morridm-zz/drumlights/images/20171210_095043.jpg

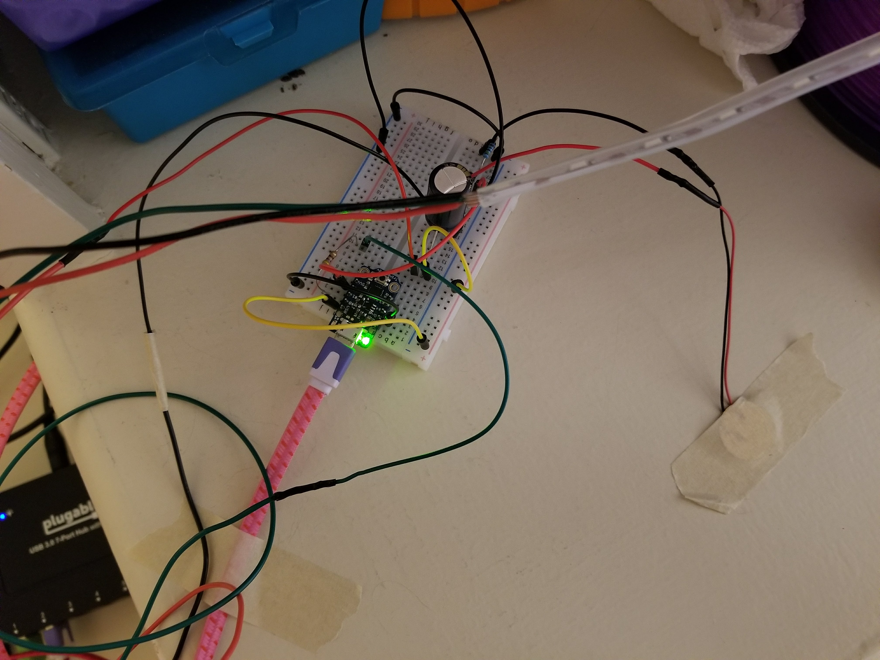
images/20171210_095043.jpg
