morridm-zz/drumlights/images/20171210_095117.jpg

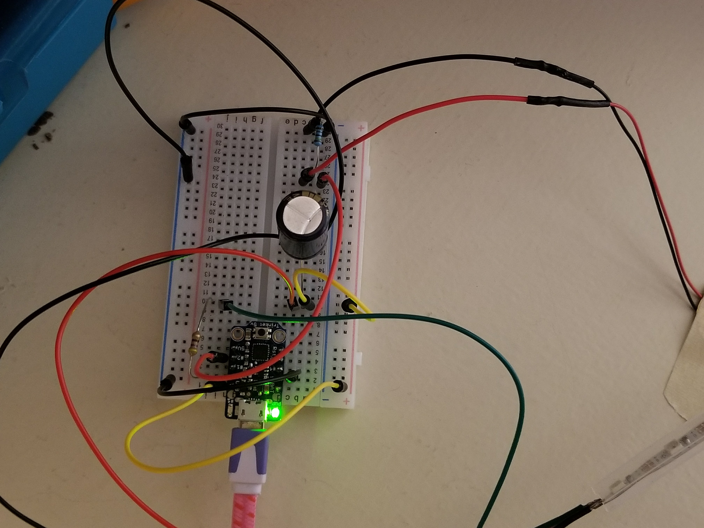
images/20171210_095117.jpg
