morridm-zz/drumlights/images/20171210_095211.jpg

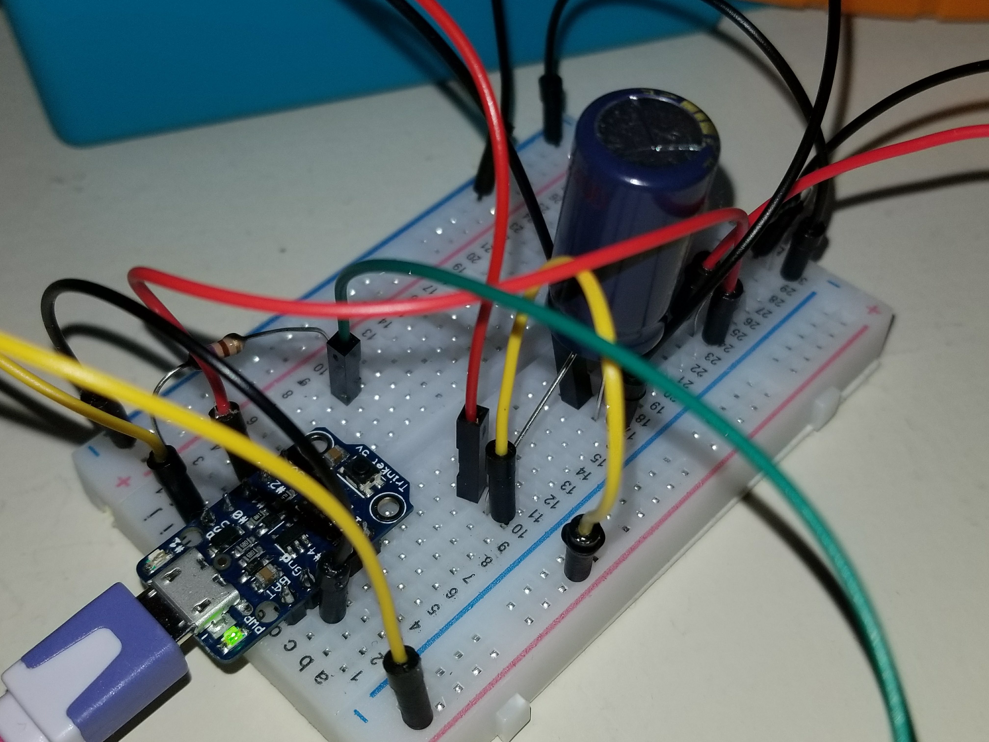
images/20171210_095211.jpg
