morridm-zz/drumlights/images/20171215_211000.jpg

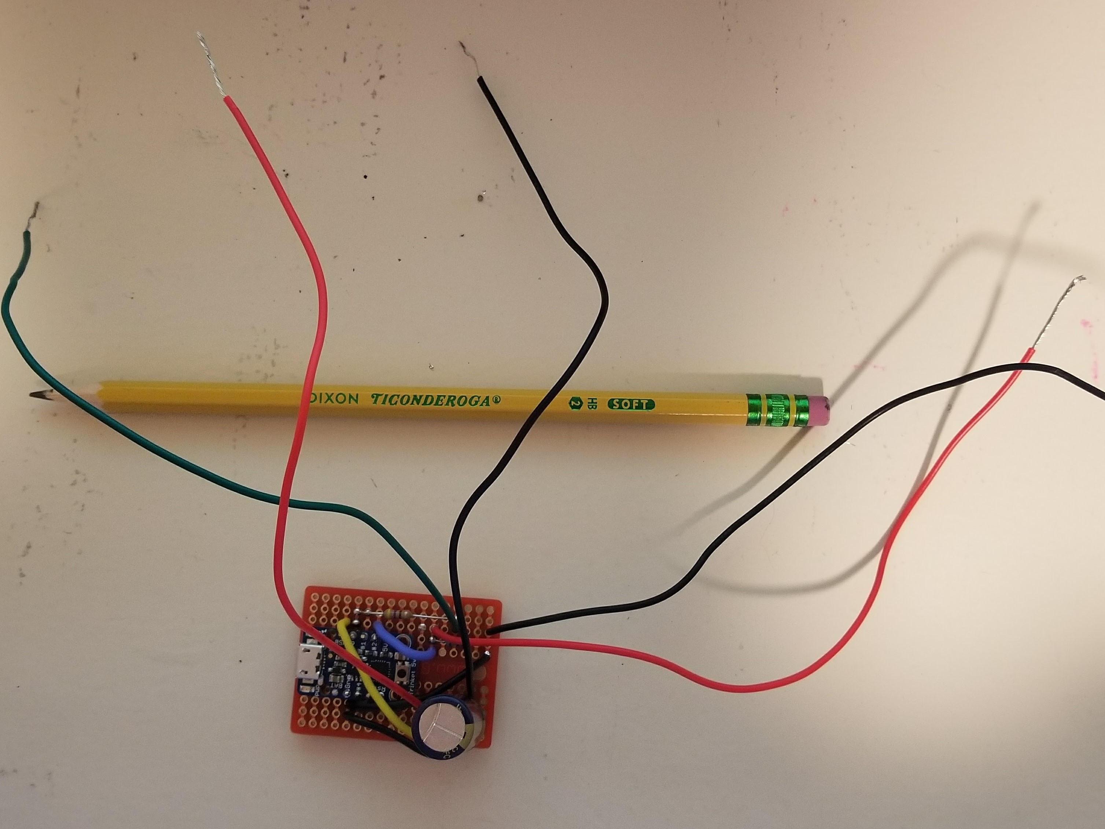
images/20171215_211000.jpg
