morridm-zz/drumlights/images/20171215_211049.jpg

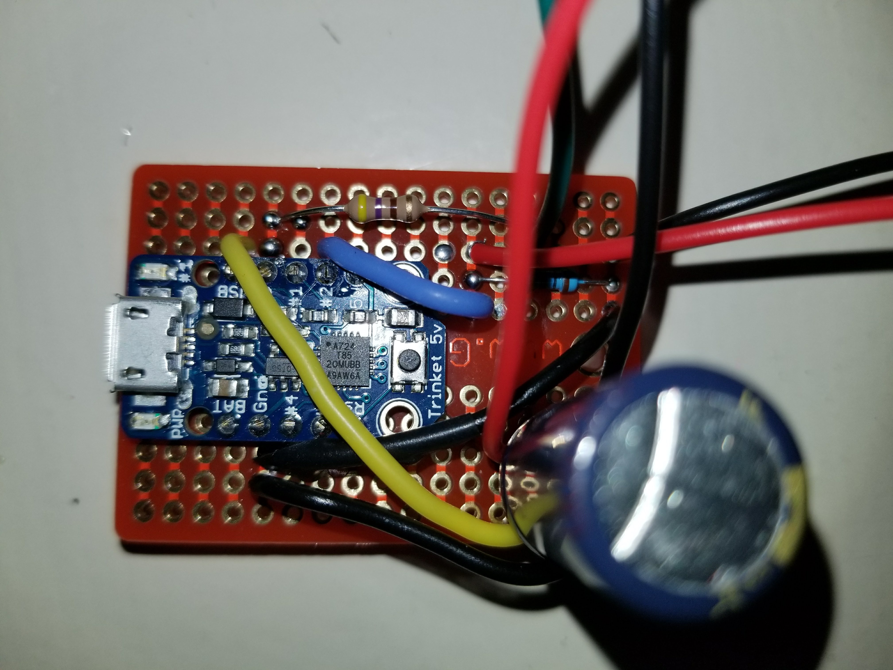
images/20171215_211049.jpg
