morridm-zz/drumlights/images/20171215_211127.jpg

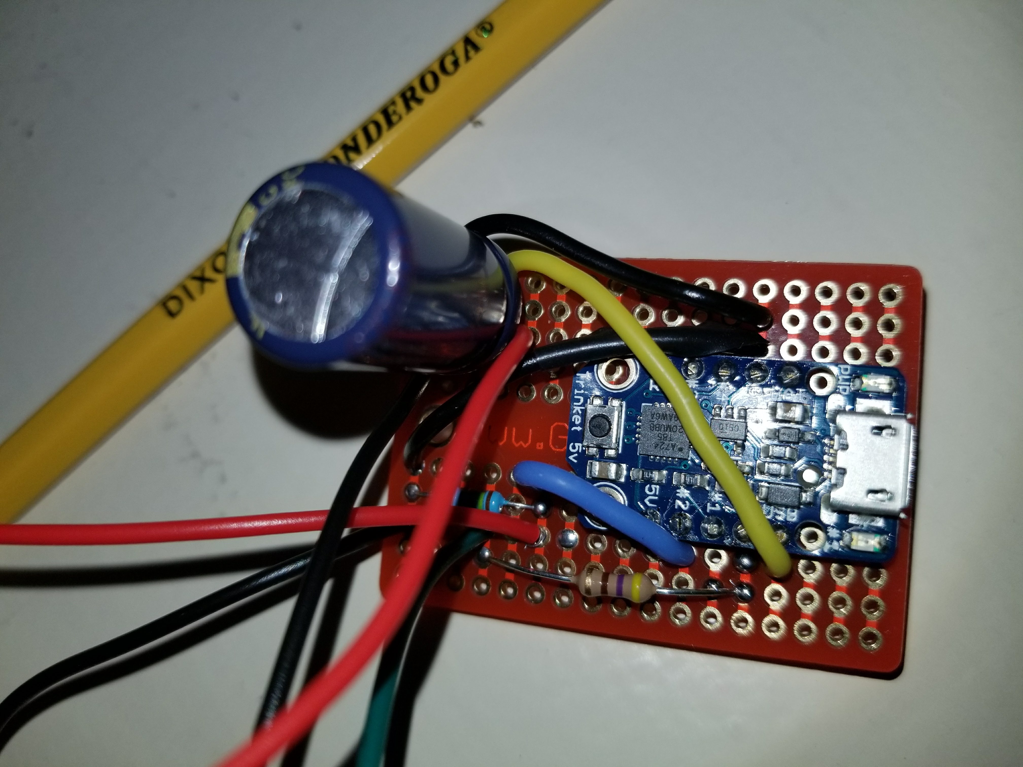
images/20171215_211127.jpg
