morridm-zz/drumlights/images/20171215_211135.jpg

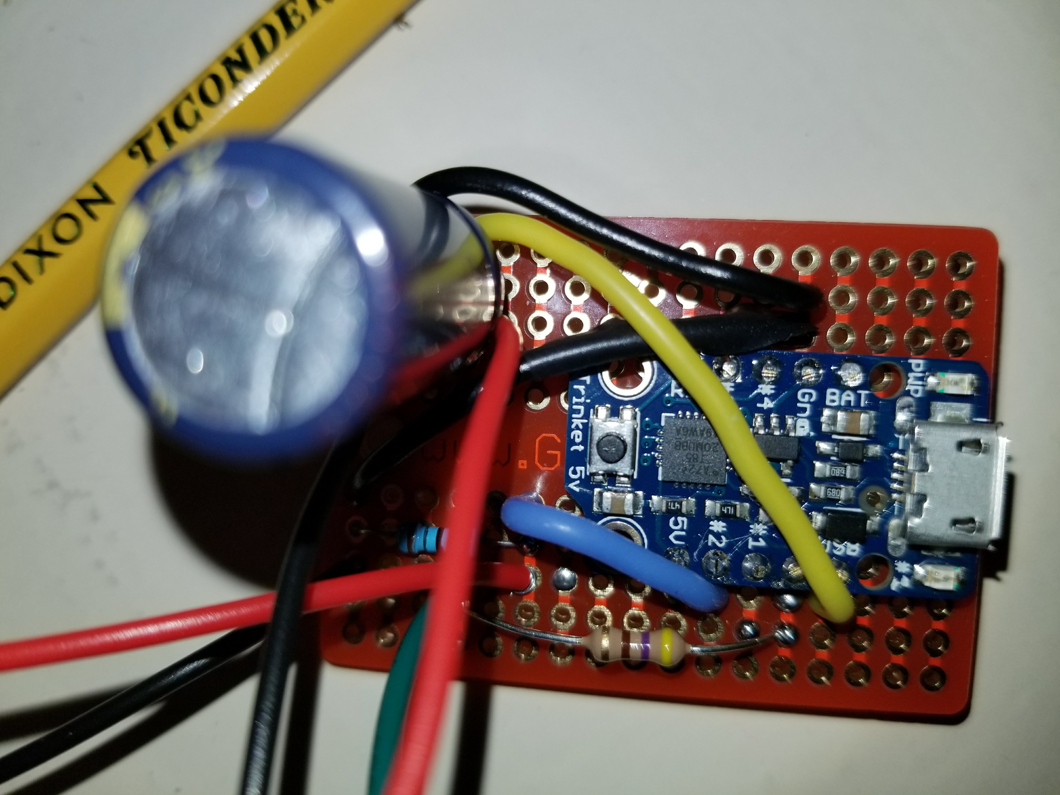
images/20171215_211135.jpg
