morridm-zz/drumlights/images/20171225_204703.jpg

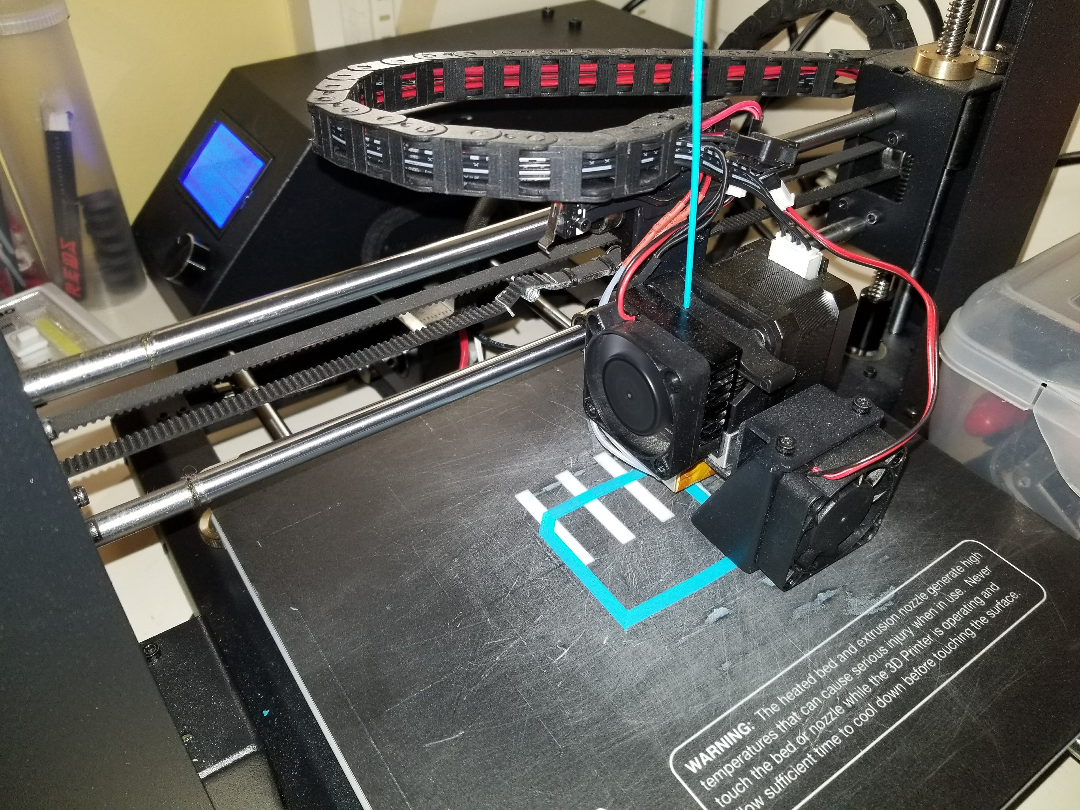
images/20171225_204703.jpg
