morridm-zz/drumlights/images/20180106_175012.jpg

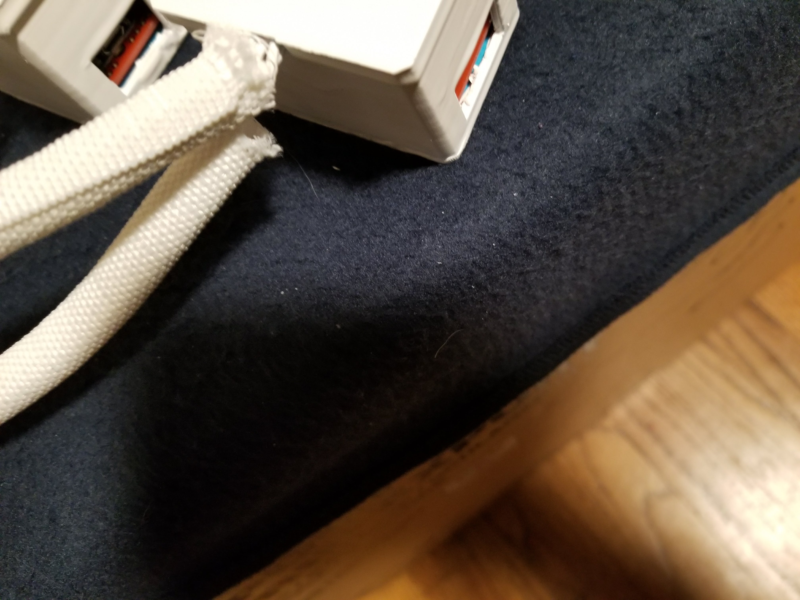
images/20180106_175012.jpg
