morridm-zz/drumlights/images/20180225_205714.jpg

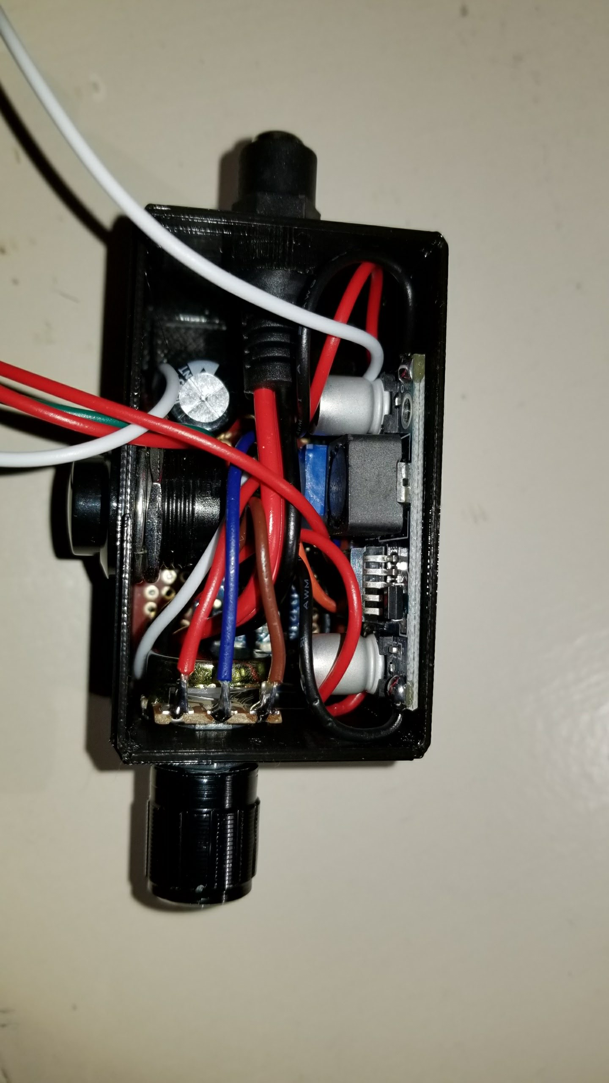
images/20180225_205714.jpg
