morridm-zz/drumlights/images/20180306_204208.jpg

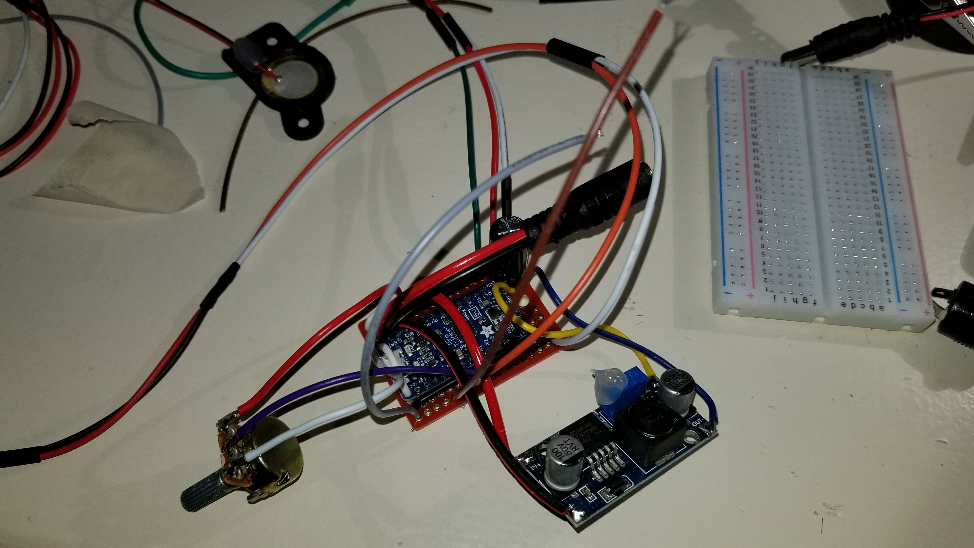
images/20180306_204208.jpg
