morridm-zz/drumlights/images/DrumLightImageAnimation.gif

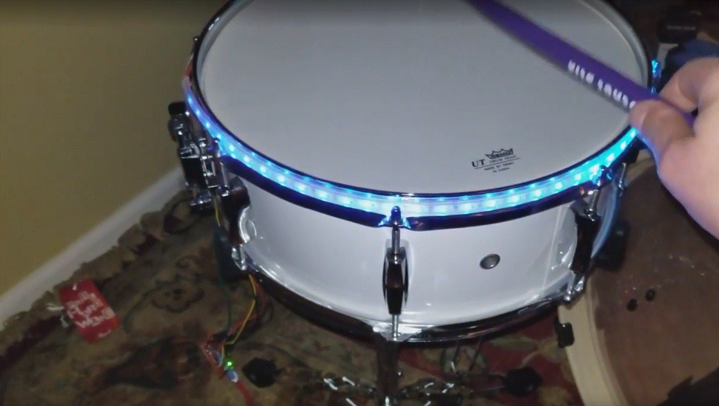
images/DrumLightImageAnimation.gif
