morridm-zz/drumlights/images/KnockSensor_480x480-3026.Jpg

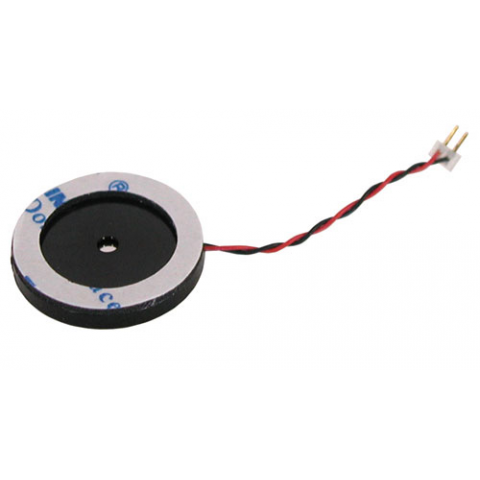
images/KnockSensor_480x480-3026.Jpg
