morridm-zz/drumlights/images/KnockSensorOriginal.jpg

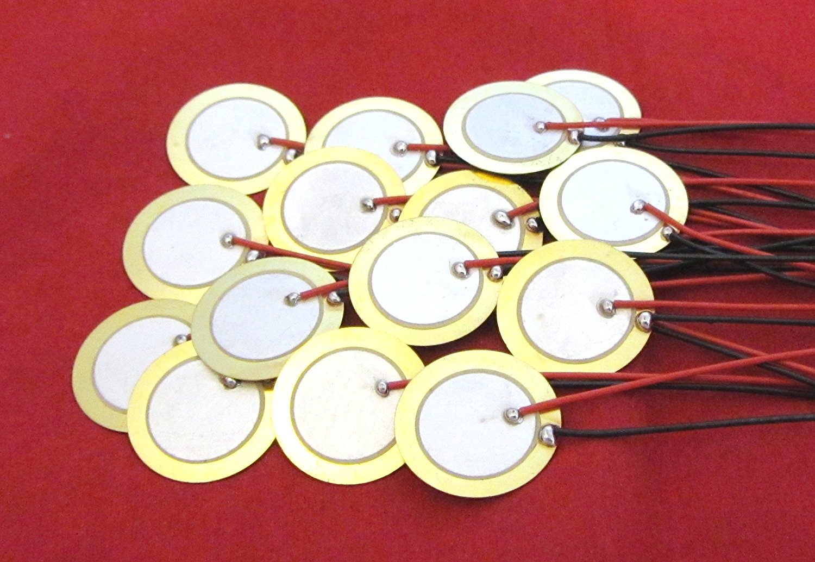
images/KnockSensorOriginal.jpg
